flrs/vpn_remote_control_gadget/docs/front.jpg

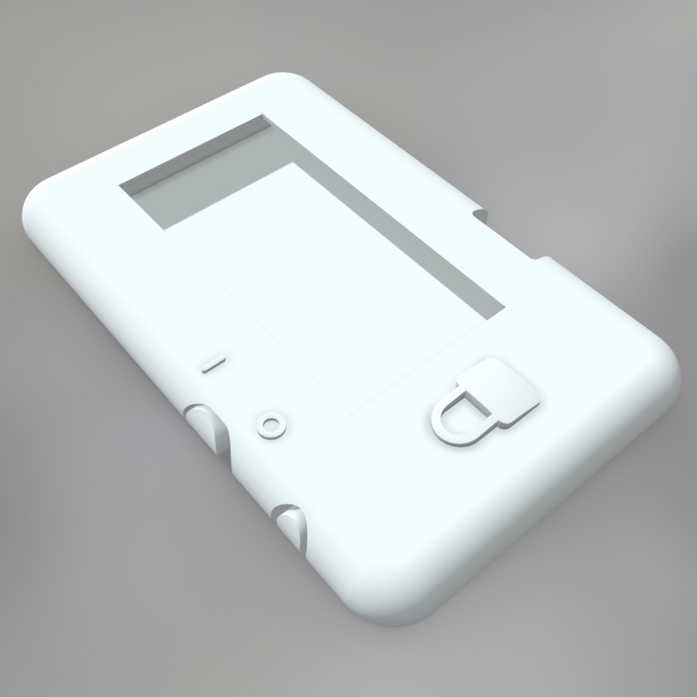
docs/front.jpg
