flrs/vpn_remote_control_gadget/arduino/vpn_remote_control_gadget/credentials_template.h

#ifndef __CREDENTIALS_H__
#define __CREDENTIALS_H__

// WiFi network settings
char server_address[] = "192.168.1.1";
char ssid[]         = ""; // TODO: Put your WiFi SSID here
char passphrase[]   = ""; // TODO: Put your WiFi passphrase here

// Router login credentials
char login_credentials[] = "user:password"; // TODO: Replace user and password by your router login credentials

#endif
